jrmrtns/galaxis/Galaxis/include/game-state.h

//
// Created by jmartens on 21.04.2023.
//

#ifndef PICOLAXIS_GAME_STATE_H
#define PICOLAXIS_GAME_STATE_H

enum gameState {
    idle, gameOver
};

enum gameType {
    single_board, multi_board
};

#endif //PICOLAXIS_GAME_STATE_H
