jrmrtns/galaxis/Galaxis/include/galaxis_game_model.h

//
// Created by jmartens on 17.10.2023.
//

#ifndef GALAXIS_GALAXIS_GAME_MODEL_H
#define GALAXIS_GALAXIS_GAME_MODEL_H

#include <cstdio>
#include "subject.h"
#include "WString.h"
#include "settings.h"

class GalaxisGameModel : public Subject {
public:
    explicit GalaxisGameModel();

    uint8_t getLastSearchResult() const;

    void setLastSearchResult(uint8_t lastSearchResult);

    uint8_t getX() const;

    void setCoordinates(uint8_t x, uint8_t y);

    uint8_t getY() const;

    uint8_t getShipCount(uint8_t id) const;

    void setShipCount(uint8_t id, uint8_t shipCount);

    uint8_t getMe() const;

    void setMe(uint8_t me);

    uint8_t getCurrent() const;

    void setCurrent(uint8_t current);

    void reset();

    bool isGameOver() const;

    void setGameOver(bool gameOver);

    bool isConnected() const;

    void setConnected(bool connected);

    const String &getHint() const;

    void setHint(const String &hint);

    bool isActive() const;

    bool isStarted() const;

    void setStarted(bool started);

    bool isSearching() const;

    void setSearching(bool searching);

    bool isWinner() const;

    void setWinner(bool won);

    uint8_t getRound() const;

    void setRound(uint8_t round);

private:
    uint8_t _me = 0;
    uint8_t _current = 0;
    uint8_t _x = 0;
    uint8_t _y = 0;
    uint8_t _shipCount[MAX_PLAYERS];
    uint8_t _lastSearchResult = 0xfa;
    String _hint = "";
    bool _connected = false;
    bool _gameOver = false;
    bool _winner = false;
    bool _started = false;
    bool _searching = false;
    uint8_t _round = 0;
};


#endif //GALAXIS_GALAXIS_GAME_MODEL_H
