jrmrtns/galaxis/Galaxis/include/ble_device_game.h

//
// Created by jmartens on 17.10.2023.
//

#ifndef GALAXIS_BLE_DEVICE_GAME_H
#define GALAXIS_BLE_DEVICE_GAME_H

#include "subject.h"
#include "abstract-game.h"
#include "galaxis.h"
#include <ArduinoBLE.h>
#include <memory>

class BLEDeviceGame : public AbstractGame {
public:
    BLEDeviceGame();

    static BLEDeviceGame *getInstance();

    ~BLEDeviceGame() override;

    void startGame() override;

private:
    static BLEDeviceGame *_instance;

    static void peripheralConnectHandler(BLEDevice central);

    static void peripheralDisconnectHandler(BLEDevice central);

    static void galaxisCharacteristicWritten(BLEDevice central, BLECharacteristic characteristic);

    static void galaxisCharacteristicSubscribed(BLEDevice central, BLECharacteristic characteristic);

    void makeGuess(uint8_t playerId, uint8_t x, uint8_t y) override;

    void NotifyUiConnected(bool connected);

    static void logMessage(const GalaxisMessage &galaxisMessage);
};

#endif //GALAXIS_BLE_DEVICE_GAME_H
