jrmrtns/galaxis/Galaxis/include/tone.h

//
// Created by jmartens on 07.05.2024.
//

#ifndef GALAXIS_TONE_H
#define GALAXIS_TONE_H

#include <memory>
#include <queue>
#include <cstdint>

typedef struct Tone {
    int  pitch;
    int duration;
} Tone;

#endif //GALAXIS_TONE_H
